sperly/Zyntheth/Software/zyntheth-midi/src/main.cpp

#include "Arduino.h"
#include <FlexCAN_T4.h>

FlexCAN_T4<CAN2, RX_SIZE_256, TX_SIZE_16> Can;

void canSniff(const CAN_message_t& msg)
{
    Serial.print("MB ");
    Serial.print(msg.mb);
    Serial.print("  OVERRUN: ");
    Serial.print(msg.flags.overrun);
    Serial.print("  LEN: ");
    Serial.print(msg.len);
    Serial.print(" EXT: ");
    Serial.print(msg.flags.extended);
    Serial.print(" TS: ");
    Serial.print(msg.timestamp);
    Serial.print(" ID: ");
    Serial.print(msg.id, HEX);
    Serial.print(" Buffer: ");
    for (uint8_t i = 0; i < msg.len; i++)
    {
        Serial.print(msg.buf[i], HEX);
        Serial.print(" ");
    }
    Serial.println();
}

void setup(void)
{
    Serial.begin(115200);
    delay(400);
    // pinMode(6, OUTPUT);
    // digitalWrite(6, LOW); /* optional tranceiver enable pin */
    Can.begin();
    Can.setBaudRate(1000000);
    Can.setMaxMB(16);
    Can.enableFIFO();
    Can.enableFIFOInterrupt();
    Can.onReceive(canSniff);
    Can.mailboxStatus();
}

void loop()
{
    Can.events();

    // static uint32_t timeout = millis();
    // if (millis() - timeout > 200)
    // {
    //     CAN_message_t msg;
    //     msg.id = random(0x1, 0x7FE);
    //     for (uint8_t i = 0; i < 8; i++) msg.buf[i] = i + 1;
    //     Can0.write(msg);
    //     timeout = millis();
    // }
}
