sperly/Zyntheth/Software/zyntheth-controller/src/menuactions/oscmenu.cpp

#include "oscmenu.hpp"
#include "config.hpp"
#include "gfx.hpp"
#include "ili9341_t3n_font_Arial.h"
#include "ili9341_t3n_font_ArialBold.h"
#include "log.hpp"

OscMenu::OscMenu(ValueContainer& valcon, uint8_t id) : vc{valcon}, oscid{id}
{
}

void OscMenu::Enter()
{
    drawMenu();
}

void OscMenu::HandleParameterChange(uint8_t parameter, int16_t value)
{
    LOG_DEBUG("Osc[%d]Menu::HandleParameterChange: par: %d, val: %d", oscid, parameter, value);
    switch (parameter)
    {
        case 1: {
            if (value > 0 && vc.oscillator[oscid].waveform < WAVEFORM_SAMPLE_HOLD)
            {
                vc.oscillator[oscid].waveform++;
            }
            else if (value < 0 && vc.oscillator[oscid].waveform > WAVEFORM_SINE)
            {
                vc.oscillator[oscid].waveform--;
            }
            LOG_DEBUG("Osc.wave: %d", vc.oscillator[oscid].waveform);
            drawWaveform();
            break;
        }
        case 2: {
            if (value > 0)
            {
                vc.oscillator[oscid].amplitude += (float_t)((float_t)value / 20.0);
            }
            else
            {
                if (vc.oscillator[oscid].amplitude > 0.05)
                    vc.oscillator[oscid].amplitude += (float_t)((float_t)value / 20.0);
                else
                    vc.oscillator[oscid].amplitude = 0;
            }
            LOG_DEBUG("Osc.amp: %.02f", vc.oscillator[oscid].amplitude);
            drawData();
            break;
        }
        case 3: {
            if (value > 0)
            {
                vc.oscillator[oscid].freqMod += (float_t)((float_t)value / 20.0);
            }
            else
            {
                if (vc.oscillator[oscid].freqMod > 0.05)
                    vc.oscillator[oscid].freqMod += (float_t)((float_t)value / 20.0);
                else
                    vc.oscillator[oscid].freqMod = 0;
            }
            LOG_DEBUG("Osc.freqMod: %.02f", vc.oscillator[oscid].freqMod);
            drawData();
            break;
        }
        case 4: {
            if (value > 0)
            {
                vc.oscillator[oscid].phaseMod += (float_t)((float_t)value / 20.0);
            }
            else
            {
                if (vc.oscillator[oscid].phaseMod > 0.05)
                    vc.oscillator[oscid].phaseMod += (float_t)((float_t)value / 20.0);
                else
                    vc.oscillator[oscid].phaseMod = 0;
            }
            LOG_DEBUG("Osc.phaphaseModse: %.02f", vc.oscillator[oscid].phaseMod);
            drawData();
            break;
        }

        default: {
            break;
        }
    }
}

void OscMenu::drawMenu()
{
    LOG_DEBUG("Drawing OscMenu[%d] menu...", oscid);
    drawHeader();
    vc.lcdHandler.fillRect(DATA_X, DATA_Y, DATA_VALUE_X - DATA_X, FOOTER_Y - DATA_Y, ILI9341_WHITE);
    vc.lcdHandler.setTextSize(14);
    vc.lcdHandler.setFont(Arial_14_Bold);
    vc.lcdHandler.setTextColor(ILI9341_BLACK);
    vc.lcdHandler.setCursor(DATA_X, DATA_Y);
    vc.lcdHandler.printf("Ampl.:");
    vc.lcdHandler.setCursor(DATA_X, DATA_Y + DATA_SPACING);
    vc.lcdHandler.printf("Frq.Mod.:");
    vc.lcdHandler.setCursor(DATA_X, DATA_Y + (2 * DATA_SPACING));
    vc.lcdHandler.printf("Phase:");

    drawData();
    drawWaveform();
    drawFooter();
}

void OscMenu::drawHeader()
{
    vc.lcdHandler.fillRect(HEADER_WIDTH, 4, 150, HEADER_HEIGHT - 6, ILI9341_WHITE);
    vc.lcdHandler.setTextSize(16);
    vc.lcdHandler.setFont(Arial_16_Bold);
    vc.lcdHandler.setTextColor(ILI9341_BLUE);
    int width = vc.lcdHandler.strPixelLen("OSC X", 5);
    vc.lcdHandler.setCursor(vc.lcdHandler.width() - 10 - width, HEADER_HEIGHT - 6 - 18);
    vc.lcdHandler.printf("OSC %d", oscid + 1);
}

void OscMenu::drawData()
{
    vc.lcdHandler.fillRect(DATA_VALUE_X - 60, DATA_Y, 60, FOOTER_Y - DATA_Y, ILI9341_WHITE);
    vc.lcdHandler.setTextSize(14);
    vc.lcdHandler.setFont(Arial_14_Bold);

    vc.lcdHandler.setTextColor(ILI9341_DARKGREY);
    int width = vc.lcdHandler.strPixelLen("W.WW", 4);
    vc.lcdHandler.setCursor(DATA_VALUE_X + 5 - width, DATA_Y);
    vc.lcdHandler.printf("%.02f", vc.oscillator[oscid].amplitude);
    vc.lcdHandler.setCursor(DATA_VALUE_X + 5 - width, DATA_Y + DATA_SPACING);
    vc.lcdHandler.printf("%.02f", vc.oscillator[oscid].freqMod);
    vc.lcdHandler.setCursor(DATA_VALUE_X + 5 - width, DATA_Y + (2 * DATA_SPACING));
    vc.lcdHandler.printf("%.02f", vc.oscillator[oscid].phaseMod);
}

void OscMenu::drawWaveform()
{
    vc.lcdHandler.fillRect(DATA_VALUE_X, DATA_Y, vc.lcdHandler.width() - DATA_VALUE_X, FOOTER_Y - DATA_Y, ILI9341_WHITE);
    switch (vc.oscillator[oscid].waveform)
    {
        case WAVEFORM_SINE:
            GFX::DrawBMP(vc, "sine.bmp", DATA_VALUE_X, DATA_Y, vc.lcdHandler);
            break;
        case WAVEFORM_SAWTOOTH:
            GFX::DrawBMP(vc, "saw.bmp", DATA_VALUE_X, DATA_Y, vc.lcdHandler);
            break;
        case WAVEFORM_SAWTOOTH_REVERSE:
            GFX::DrawBMP(vc, "saw-rev.bmp", DATA_VALUE_X, DATA_Y, vc.lcdHandler);
            break;
        case WAVEFORM_SQUARE:
            GFX::DrawBMP(vc, "square.bmp", DATA_VALUE_X, DATA_Y, vc.lcdHandler);
            break;
        case WAVEFORM_TRIANGLE:
            GFX::DrawBMP(vc, "tri.bmp", DATA_VALUE_X, DATA_Y, vc.lcdHandler);
            break;
        case WAVEFORM_TRIANGLE_VARIABLE:
            GFX::DrawBMP(vc, "tri-var.bmp", DATA_VALUE_X, DATA_Y, vc.lcdHandler);
            break;
        case WAVEFORM_ARBITRARY:
            GFX::DrawBMP(vc, "arb.bmp", DATA_VALUE_X, DATA_Y, vc.lcdHandler);
            break;
        case WAVEFORM_PULSE:
            GFX::DrawBMP(vc, "pulse.bmp", DATA_VALUE_X, DATA_Y, vc.lcdHandler);
            break;
        case WAVEFORM_SAMPLE_HOLD:
            GFX::DrawBMP(vc, "sample.bmp", DATA_VALUE_X, DATA_Y, vc.lcdHandler);
            break;
        default:
            break;
    }
}

void OscMenu::drawFooter()
{
    vc.lcdHandler.setTextSize(14);
    vc.lcdHandler.setFont(Arial_14_Bold);

    vc.lcdHandler.fillRect(DATA_X, FOOTER_Y, vc.lcdHandler.width() - 10, FOOTER_Y + 20, ILI9341_WHITE);
    vc.lcdHandler.drawFastHLine(DATA_X, FOOTER_Y, vc.lcdHandler.width() - (2 * DATA_X), ILI9341_BLACK);

    GFX::DrawBMP(vc, "arrow_l.bmp", DATA_X, FOOTER_Y + 9, vc.lcdHandler);
    vc.lcdHandler.setCursor(DATA_X + 20, FOOTER_Y + 9);
    vc.lcdHandler.setTextColor(ILI9341_BLACK);
    vc.lcdHandler.printf("Osc. Contr.");

    GFX::DrawBMP(vc, "arrow_r.bmp", vc.lcdHandler.width() - 30, FOOTER_Y + 9, vc.lcdHandler);
    vc.lcdHandler.setCursor(vc.lcdHandler.width() - 35 - vc.lcdHandler.strPixelLen("Filter", 6), FOOTER_Y + 9);
    vc.lcdHandler.setTextColor(ILI9341_BLACK);
    vc.lcdHandler.printf("Filter");
}
