sperly/Zyntheth/Software/zyntheth-controller/src/log.hpp

#pragma once

#include "Arduino.h"

/*
 * Copyright (c) 2012 David Rodrigues
 *
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
 * THE SOFTWARE IS PROVIDED "AS IS", WITHOUT WARRANTY OF ANY KIND, EXPRESS
 * OR IMPLIED, INCLUDING BUT NOT LIMITED TO THE WARRANTIES OF MERCHANTABILITY,
 * FITNESS FOR A PARTICULAR PURPOSE AND NONINFRINGEMENT. IN NO EVENT SHALL THE
 * AUTHORS OR COPYRIGHT HOLDERS BE LIABLE FOR ANY CLAIM, DAMAGES OR OTHER
 * LIABILITY, WHETHER IN AN ACTION OF CONTRACT, TORT OR OTHERWISE, ARISING
 * FROM, OUT OF OR IN CONNECTION WITH THE SOFTWARE OR THE USE OR OTHER DEALINGS
 * IN THE SOFTWARE.
 */

#ifndef __MACROLOGGER_H__
#    define __MACROLOGGER_H__

#    include <string.h>

#    define _FILE strrchr(__FILE__, '/') ? strrchr(__FILE__, '/') + 1 : __FILE__

#    define NO_LOG 0x00
#    define ERROR_LEVEL 0x01
#    define INFO_LEVEL 0x02
#    define DEBUG_LEVEL 0x03

#    ifndef LOG_LEVEL
#        define LOG_LEVEL DEBUG_LEVEL
#    endif

#    define PRINTFUNCTION(format, ...) Serial.printf(format, __VA_ARGS__)

#endif

#define LOG_FMT "%-5s | %-15s | %s:%d | "
#define LOG_ARGS(LOG_TAG) LOG_TAG, _FILE, __FUNCTION__, __LINE__

#define NEWLINE "\n\r"

#define ERROR_TAG "ERROR"
#define INFO_TAG "INFO"
#define DEBUG_TAG "DEBUG"

#if LOG_LEVEL >= DEBUG_LEVEL
#    define LOG_DEBUG(message, args...) PRINTFUNCTION(LOG_FMT message NEWLINE, LOG_ARGS(DEBUG_TAG), ##args)
#else
#    define LOG_DEBUG(message, args...)
#endif

#if LOG_LEVEL >= INFO_LEVEL
#    define LOG_INFO(message, args...) PRINTFUNCTION(LOG_FMT message NEWLINE, LOG_ARGS(INFO_TAG), ##args)
#else
#    define LOG_INFO(message, args...)
#endif

#if LOG_LEVEL >= ERROR_LEVEL
#    define LOG_ERROR(message, args...) PRINTFUNCTION(LOG_FMT message NEWLINE, LOG_ARGS(ERROR_TAG), ##args)
#else
#    define LOG_ERROR(message, args...)
#endif
