sperly/Zyntheth/Software/zyntheth-controller/src/menuhandler.cpp

#include "menuhandler.hpp"
#include <memory>
#include "log.hpp"
#include "menuActions/adsr.hpp"
#include "menuActions/menuaction.hpp"
#include "menuActions/oscmain.hpp"
#include "menuActions/oscmenu.hpp"
#include "menuactions/splashmenu.hpp"
#include "menuactions/testmenu.hpp"

MenuHandler::MenuHandler() : menuStack{}, menu{}, currentMenuIndex{0}
{
}

void MenuHandler::Init(ValueContainer& valuecon)
{
    LOG_DEBUG("Initializing menuhandler...");
    menu.emplace_back(new SplashMenu{valuecon});
    menu.emplace_back(new TestMenu{valuecon});
    menu.emplace_back(new OscMain{valuecon});
    menu.back()->SubMenu.emplace_back(new OscMenu{valuecon, 0});
    menu.back()->SubMenu.back()->SubMenu.emplace_back(new ADSR{valuecon, 0});
    menu.back()->SubMenu.emplace_back(new OscMenu{valuecon, 1});
    menu.back()->SubMenu.back()->SubMenu.emplace_back(new ADSR{valuecon, 1});
    menu.back()->SubMenu.emplace_back(new OscMenu{valuecon, 2});
    menu.back()->SubMenu.back()->SubMenu.emplace_back(new ADSR{valuecon, 2});
    menu.back()->SubMenu.emplace_back(new OscMenu{valuecon, 3});
    menu.back()->SubMenu.back()->SubMenu.emplace_back(new ADSR{valuecon, 3});

    menuStack.push_back(std::make_unique<std::vector<IMenuAction*>>(menu));
    menuStack.back()->at(0)->Enter();
    LOG_DEBUG("Initializing menuhandler done.");
}

void MenuHandler::HandleMenuAction(uint8_t parameter, int16_t value)
{
    LOG_DEBUG("par: %d, val: %d (currMenu = %d/%d)", parameter, value, currentMenuIndex.back(), menuStack.back()->size());
    if (parameter == 0)
    {
        if (value < 0)
        {
            if (currentMenuIndex.back() > 0)
                currentMenuIndex.back()--;
            else
                currentMenuIndex.back() = menuStack.back()->size() - 1;
        }
        else
        {
            if (currentMenuIndex.back() < (menuStack.back()->size() - 1))
                currentMenuIndex.back()++;
            else
                currentMenuIndex.back() = 0;
        }

        menuStack.back()->at(currentMenuIndex.back())->Enter();
    }
    else if (parameter == 5 && value == 1)
    {
        if (menuStack.back()->at(currentMenuIndex.back())->SubMenu.size() > 0)
        {
            LOG_DEBUG("Changing to submenu");
            menuStack.push_back(std::make_unique<std::vector<IMenuAction*>>(menuStack.back()->at(currentMenuIndex.back())->SubMenu));
            currentMenuIndex.push_back(0);
            menuStack.back()->at(currentMenuIndex.back())->Enter();
        }
    }
    else if (parameter == 10 && menuStack.size() > 1 && value == 1)
    {
        LOG_DEBUG("Returning to parent menu");
        menuStack.pop_back();
        currentMenuIndex.pop_back();
        menuStack.back()->at(currentMenuIndex.back())->Enter();
    }
    else
    {
        menuStack.back()->at(currentMenuIndex.back())->HandleParameterChange(parameter, value);
    }
}
